drissimohamed/Modeling-and-design-of-Inverting-Buck-boost-/LTSpice/input filter.asc

C3: cap; 220
C4: cap; 5.45µ
C5: cap; 53.2µ
C7: cap; 220
C8: cap; 5.45µ
C9: cap; 53.2µ
I2: current; 1; AC 1
L2: ind; 10µ
L5: ind; 10µ
R2: res; 2m
R3: res; 0.411
R4: res; 0.411; pwr=1
R5: res; 2m
R6: res; 2m
R7: res; 18m
R8: res; 18m
R9: res; 2m
V1: voltage; ""; AC 1
Named nets: 0, Zout, Vout
.ac dec 201 1 10meg
