drissimohamed/Modeling-and-design-of-Inverting-Buck-boost-/LTSpice/5V Linear voltage regulator.asc

C1: cap; 1Meg
C2: cap; 20µ
C3: cap; 44µ
C4: cap; 330p
C5: cap; 247p
C6: cap; 220p
D1: diode
I1: current; PULSE(0 1 0.06 100n 100n 0.2 0.2 1)
I2: current; PULSE(0 1 0.5 100n 100n 0.2 0.2 1)
Q1: pnp; 2N3906
Q2: npn; 2N2222
Q3: npn; 2N2222A
Q4: npn; 2N2222A
Q5: npn; 2N2222A
Q6: npn; 2N2222A
Q7: npn; 2N2222A
R1: res; 10k
R2: res; 1.8K
R3: res; 68k
R4: res; 18k
R5: res; 50
R6: res; 10k
R7: res; 1.4
R8: res; 10K
R9: res; 10k
R10: res; 10
R11: res; 0.01
R12: res; 0.01
R13: res; 1k
R14: res; 220
R15: res; 10k
R16: res; 33k
R17: res; 220m
R18: res; 220m
R19: res; 1k
U1: TL431
U2: UniversalOpAmp2
V1: voltage; 24V
V2: voltage; 24V
V3: voltage; 2.5
V4: voltage; ""; AC 1
V5: voltage; PULSE(0 -12 0 10m 0 2s 2s 1)
Named nets: 0, OUT, VIN, -12
.tran 0.1
;ac dec 201 1 10meg
.param Rupper= 10k
.param fc=12k
.param Gfc=15
.param pfc=-100
.param pm=60
.param G=10^(-Gfc/10)
.param boost = pm-(pfc)-90
.param pi= 3.14159
.param k=tan((boost/2+45)*pi/180)
.param fz=fc/k
.param C2=1/(2*pi*fc*G*k*Rupper)
.param C1=C2*(k^2-1)
.param  R2=k/(2*pi*fc*C1)
.step param c list 0 47p 100p 220p 1n
