drissimohamed/Modeling-and-design-of-Inverting-Buck-boost-/LTSpice/Input switch.asc

C1: cap; 100n
C2: cap; 120µ
C3: cap; 10n
D1: zener; D816A
D2: zener; D816A
D4: zener; BZX84C5V6
M1: pmos; 2SJ554
M2: pmos; 2SJ554
Q1: pnp; 2N3906
Q2: pnp; 2N3906
Q3: npn; 2N2222
Q4: pnp; 2N3906
Q5: pnp; 2N3906
R1: res; 0.47
R2: res; 100K
R3: res; 16
R4: res; 10K
R5: res; 68k
R6: res; 100K
R9: res; 1K
R15: res; 3680
R16: res; 100K
R17: res; 100K
R18: res; 24K
R19: res; 220
R20: res; 100k
R21: res; 39K
R22: res; 100
R23: res; 100
V1: voltage; 24; Rser=0.1
Named nets: 0, Out, In, Base, Vz
.tran 0.3 startup
.param I=3
